Protsen-UN/Protsen-v1.0/Documentos Previos/ProyectoProsUN-SenPros/Imagenes/ProtosUN1.jpg

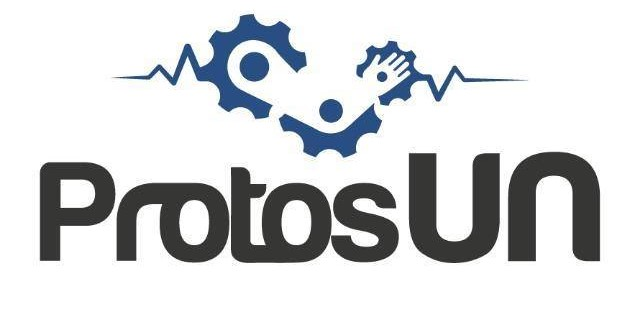
Documentos Previos/ProyectoProsUN-SenPros/Imagenes/ProtosUN1.jpg
