Protsen-UN/Protsen-v1.0/Imagenes/AplicacionCarga.jpg

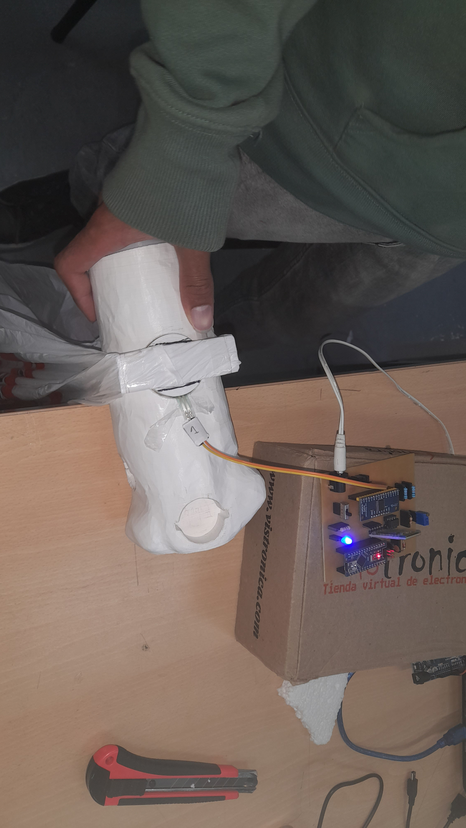
Imagenes/AplicacionCarga.jpg
