Protsen-UN/Protsen-v1.0/Imagenes/AplicacionCargaEscoba.jpg

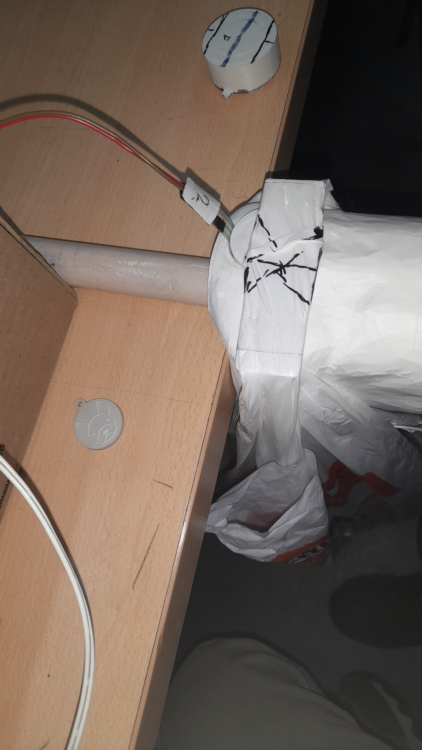
Imagenes/AplicacionCargaEscoba.jpg
