Protsen-UN/Protsen-v1.0/Imagenes/AplicacionCargaGuias.jpg

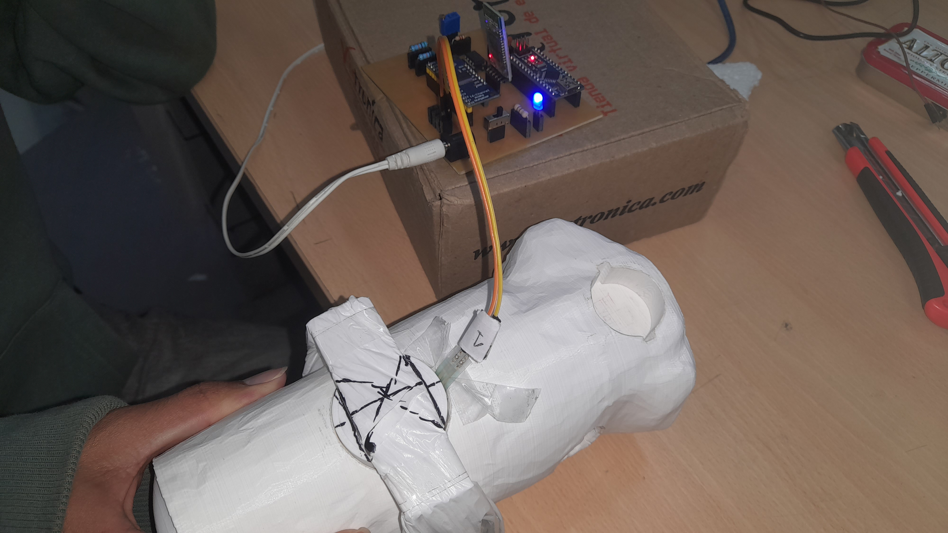
Imagenes/AplicacionCargaGuias.jpg
