Protsen-UN/Protsen-v1.0/Imagenes/ArduinoConexion.jpg

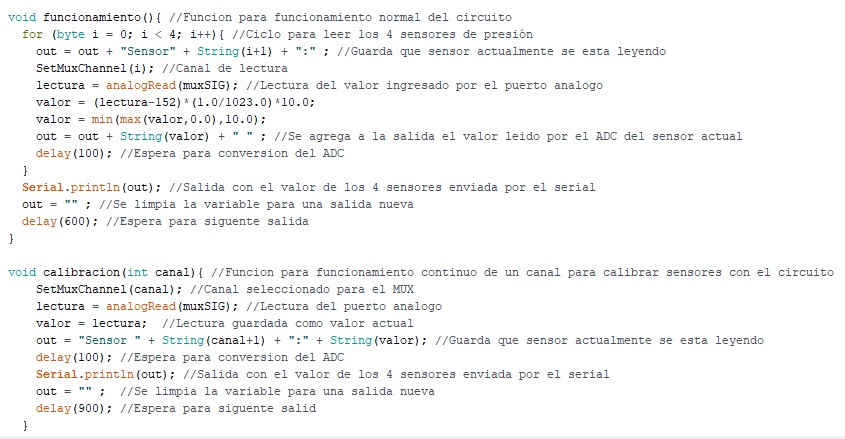
Imagenes/ArduinoConexion.jpg
