Protsen-UN/Protsen-v1.0/Imagenes/DatosBluetooth.jpg

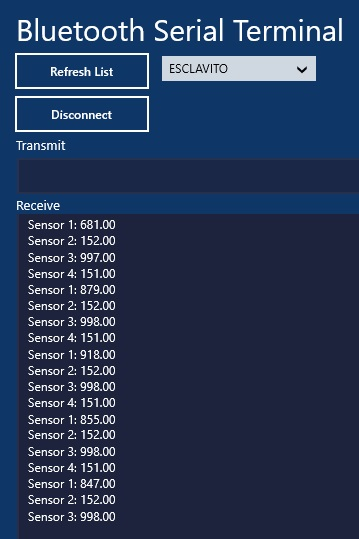
Imagenes/DatosBluetooth.jpg
