Protsen-UN/Protsen-v1.0/Imagenes/EsquematicoPCB.jpg

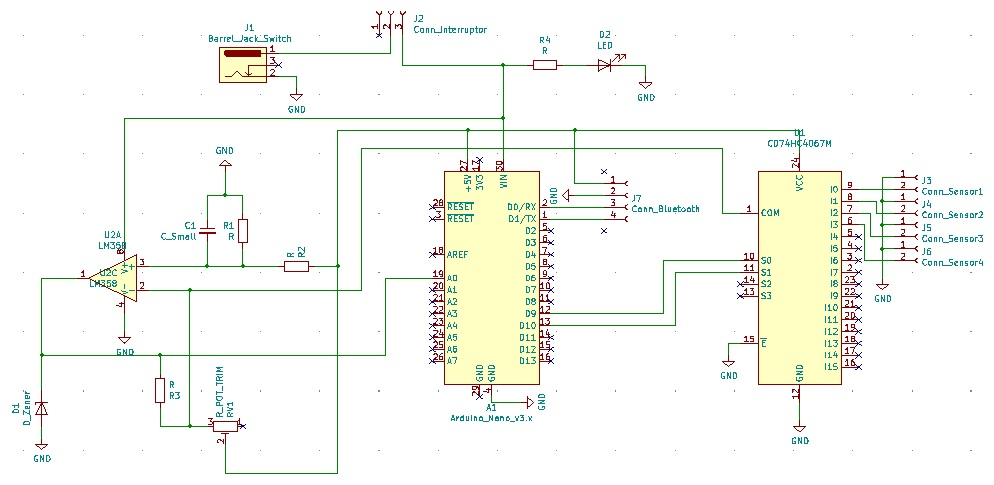
Imagenes/EsquematicoPCB.jpg
