Protsen-UN/Protsen-v1.0/Imagenes/Sensor1Histeresis.png

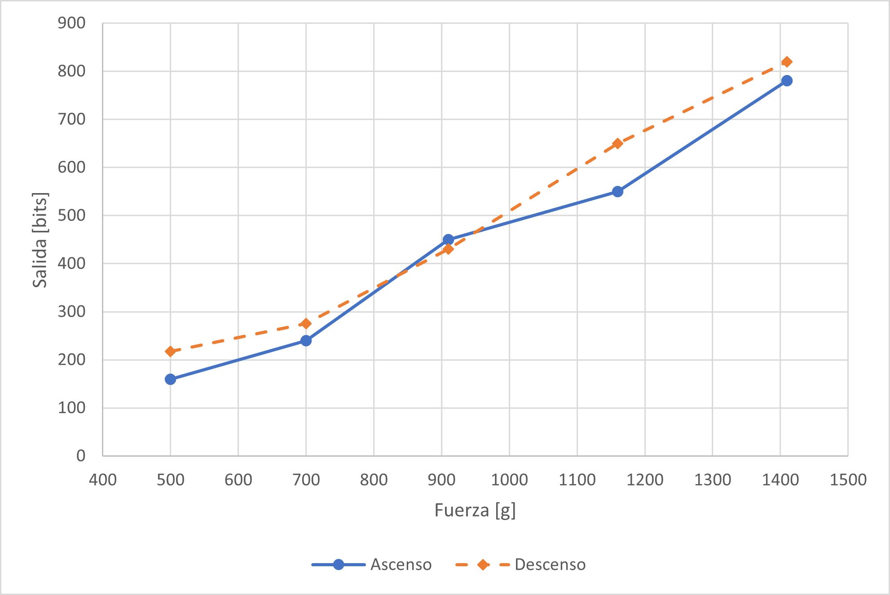
Imagenes/Sensor1Histeresis.png
