Protsen-UN/Protsen-v1.0/Imagenes/Sensor2Histeresis.png

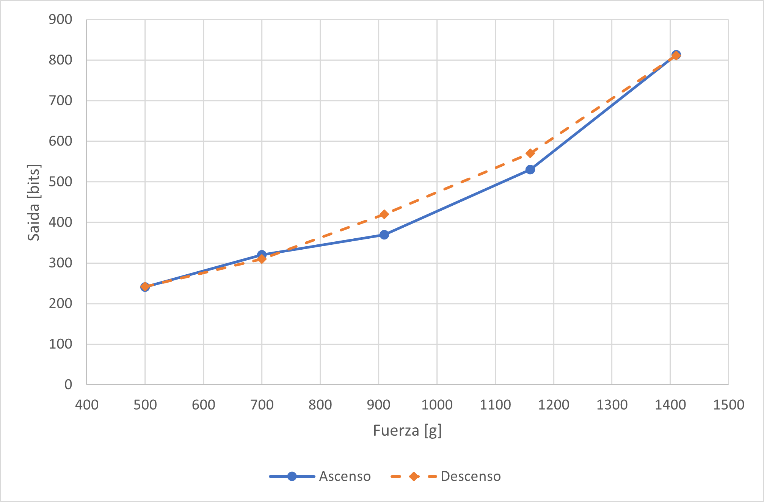
Imagenes/Sensor2Histeresis.png
