Protsen-UN/Protsen-v1.0/Imagenes/Sensor3Recta.png

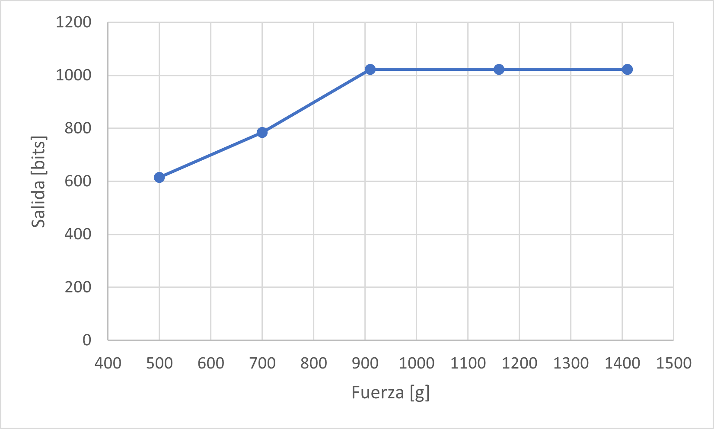
Imagenes/Sensor3Recta.png
