Protsen-UN/Protsen-v1.0/Imagenes/Sensor4Histeresis.png

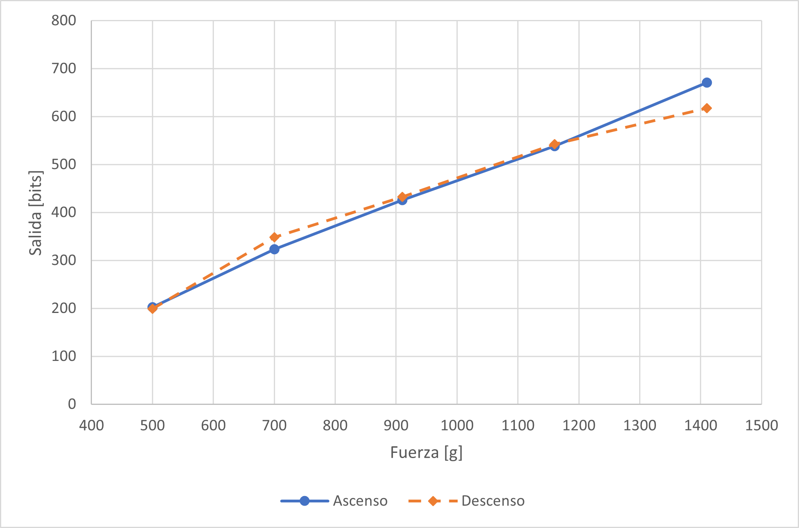
Imagenes/Sensor4Histeresis.png
