Protsen-UN/Protsen-v1.0/Imagenes/UbicacionSensorPierna.jpg

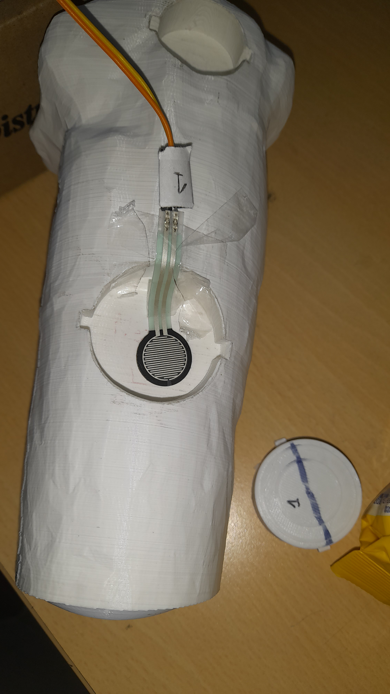
Imagenes/UbicacionSensorPierna.jpg
