Protsen-UN/Protsen-v1.0/Imagenes/MontajePCB.jpg

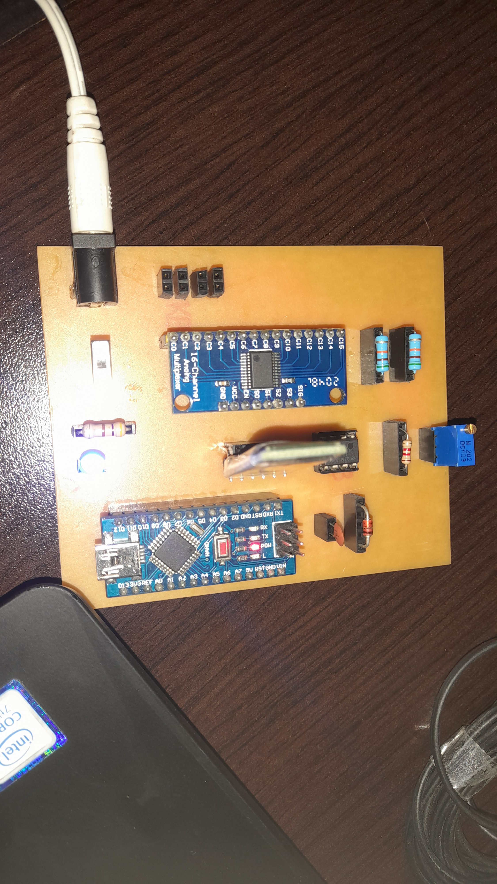
Imagenes/MontajePCB.jpg
